ashpil/Model-M-Type-C/images/keyboard.jpg

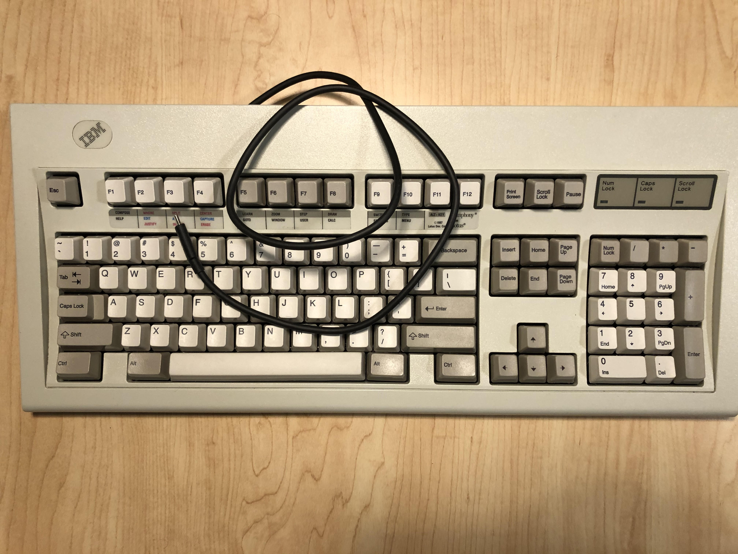
images/keyboard.jpg
