ashpil/Model-M-Type-C/images/keyboardback.jpg

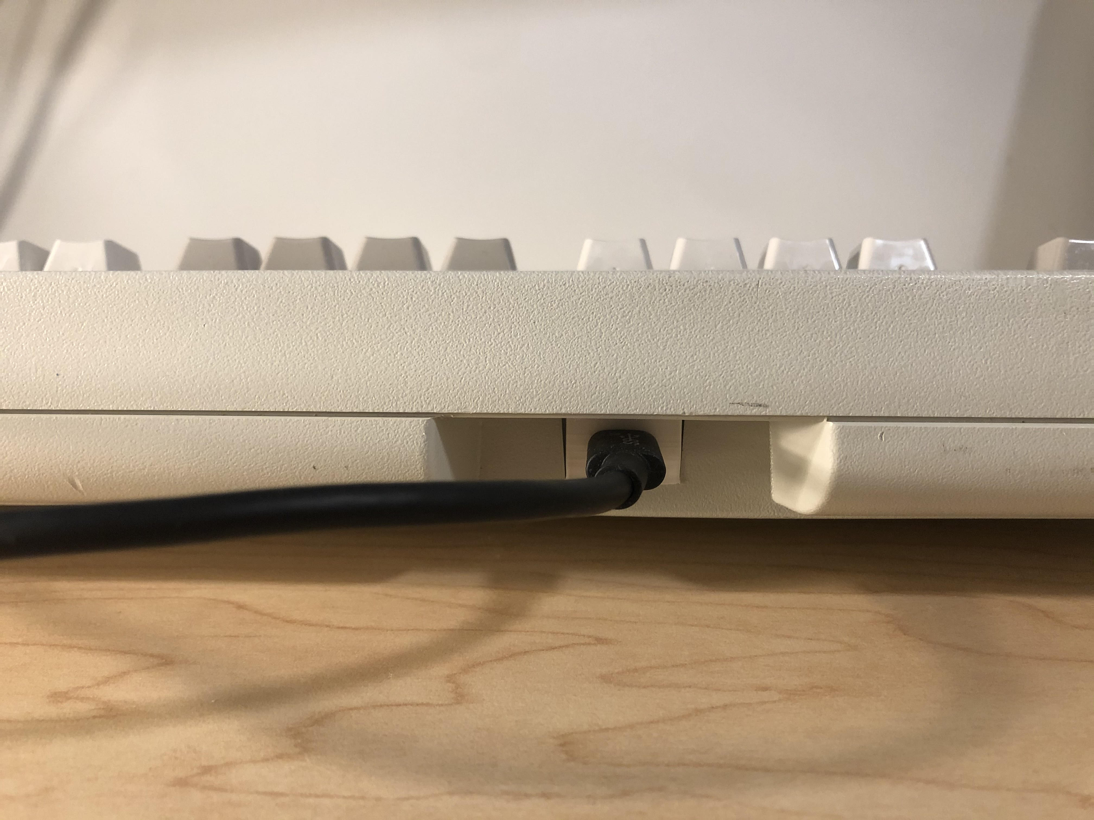
images/keyboardback.jpg
